andykarpov/nanit/firmware/Nanit_v2.1_1202_mod/nokia1100_lcd_font.h

//***************************************************************************
//  File........: nokia1100_lcd_lib.h
//  Author(s)...: Chiper
//  URL(s)......: http://digitalchip.ru/
//  Adapted for Nokia 2660/2760 by MadOrc
//***************************************************************************
#ifndef _NOKIA1100_LCD_FONT_H_
#define _NOKIA1100_LCD_FONT_H_

#include <avr/io.h>
#include <avr/eeprom.h>
#include <avr/pgmspace.h>

// Workaround for http://gcc.gnu.org/bugzilla/show_bug.cgi?id=34734
#ifdef PROGMEM
#undef PROGMEM
#define PROGMEM __attribute__((section(".progmem.data")))
#endif

#ifndef EEMEM
#define EEMEM__attribute__ ((section (".eeprom")))
#endif

//***************************************************************************
// Формат символов: 5x8. Установленный бит соответствует включенному пикселю
static unsigned char EEMEM nlcd_Font[][5] ={
//static const unsigned char nlcd_Font[][5] PROGMEM ={
	{0x00, 0x00, 0x00, 0x00, 0x00},// (space)
	{0x00, 0x00, 0x5F, 0x00, 0x00},// !
	{0x00, 0x00, 0x3C, 0x3C, 0x3C}, //bl " 
//	{0x00, 0x07, 0x00, 0x07, 0x00},// "
	{0x1C, 0x1C, 0x7F, 0x7F, 0x7F},// battL // #	
	{0x7F, 0x7F, 0x7F, 0x3E, 0x00},// battR //$
//	{0x14, 0x7F, 0x14, 0x7F, 0x14},// #
//	{0x24, 0x2A, 0x7F, 0x2A, 0x12},// $
	{0x23, 0x13, 0x08, 0x64, 0x62},// %
	{0x41, 0x22, 0x14, 0x08, 0x00},// > //& 
//	{0x36, 0x49, 0x55, 0x22, 0x50},// &
	{0x00, 0x05, 0x03, 0x00, 0x00},// '
	{0x00, 0x00, 0x7F, 0x41, 0x41},// [ // (
	{0x41, 0x41, 0x7F, 0x00, 0x00},// ] // )
//	{0x00, 0x1C, 0x22, 0x41, 0x00},// (
//	{0x00, 0x41, 0x22, 0x1C, 0x00},// )
	{0x08, 0x2A, 0x1C, 0x2A, 0x08},// *
	{0x08, 0x08, 0x3E, 0x08, 0x08},// +
	{0x00, 0x50, 0x30, 0x00, 0x00},// ,
	{0x08, 0x08, 0x08, 0x08, 0x08},// -
	{0x00, 0x30, 0x30, 0x00, 0x00},// .
	{0x20, 0x10, 0x08, 0x04, 0x02},// /
	{0x3E, 0x51, 0x49, 0x45, 0x3E},// 0
	{0x00, 0x42, 0x7F, 0x40, 0x00},// 1
	{0x42, 0x61, 0x51, 0x49, 0x46},// 2
	{0x21, 0x41, 0x45, 0x4B, 0x31},// 3
	{0x18, 0x14, 0x12, 0x7F, 0x10},// 4
	{0x27, 0x45, 0x45, 0x45, 0x39},// 5
	{0x3C, 0x4A, 0x49, 0x49, 0x30},// 6
	{0x01, 0x71, 0x09, 0x05, 0x03},// 7
	{0x36, 0x49, 0x49, 0x49, 0x36},// 8
	{0x06, 0x49, 0x49, 0x29, 0x1E},// 9
	{0x00, 0x36, 0x36, 0x00, 0x00},// :
/*	{0x00, 0x56, 0x36, 0x00, 0x00},// ;
	{0x00, 0x08, 0x14, 0x22, 0x41},// <
	{0x14, 0x14, 0x14, 0x14, 0x14},// =
	{0x41, 0x22, 0x14, 0x08, 0x00},// >
	{0x02, 0x01, 0x51, 0x09, 0x06},// ?
	{0x32, 0x49, 0x79, 0x41, 0x3E},// @
	{0x7E, 0x11, 0x11, 0x11, 0x7E},// A
	{0x7F, 0x49, 0x49, 0x49, 0x36},// B
	{0x3E, 0x41, 0x41, 0x41, 0x22},// C
	{0x7F, 0x41, 0x41, 0x22, 0x1C},// D
	{0x7F, 0x49, 0x49, 0x49, 0x41},// E
	{0x7F, 0x09, 0x09, 0x01, 0x01},// F
	{0x3E, 0x41, 0x41, 0x51, 0x32},// G
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
*/		

 	//Частично соответствует кодировке 866 до символа "п", далее - несоответствие

	{ 0x7E, 0x11, 0x11, 0x11, 0x7E },  // А
	{ 0x7F, 0x49, 0x49, 0x49, 0x33 },  // Б
	{ 0x7F, 0x49, 0x49, 0x49, 0x36 },  // В
	{ 0x7F, 0x01, 0x01, 0x01, 0x03 },  // Г
	{ 0xE0, 0x51, 0x4F, 0x41, 0xFF },  // Д
	{ 0x7F, 0x49, 0x49, 0x49, 0x49 },  // Е
	{ 0x77, 0x08, 0x7F, 0x08, 0x77 },  // Ж
	{ 0x49, 0x49, 0x49, 0x49, 0x36 },  // З
	{ 0x7F, 0x10, 0x08, 0x04, 0x7F },  // И
	{ 0x7C, 0x21, 0x12, 0x09, 0x7C },  // Й
	{ 0x7F, 0x08, 0x14, 0x22, 0x41 },  // К
	{ 0x20, 0x41, 0x3F, 0x01, 0x7F },  // Л
	{ 0x7F, 0x02, 0x0C, 0x02, 0x7F },  // М
	{ 0x7F, 0x08, 0x08, 0x08, 0x7F },  // Н
	{ 0x3E, 0x41, 0x41, 0x41, 0x3E },  // О
	{ 0x7F, 0x01, 0x01, 0x01, 0x7F },  // П
	{ 0x7F, 0x09, 0x09, 0x09, 0x06 },  // Р
	{ 0x3E, 0x41, 0x41, 0x41, 0x22 },  // С
	{ 0x01, 0x01, 0x7F, 0x01, 0x01 },  // Т
	{ 0x27, 0x48, 0x48, 0x48, 0x3F },  // У
	{ 0x1C, 0x22, 0x7F, 0x22, 0x1C },  // Ф
	{ 0x63, 0x14, 0x08, 0x14, 0x63 },  // Х
	{ 0x7F, 0x40, 0x40, 0x40, 0xFF },  // Ц
	{ 0x07, 0x08, 0x08, 0x08, 0x7F },  // Ч
	{ 0x7F, 0x40, 0x7F, 0x40, 0x7F },  // Ш
	{ 0x7F, 0x40, 0x7F, 0x40, 0xFF },  // Щ
	{ 0x01, 0x7F, 0x48, 0x48, 0x30 },  // Ъ
	{ 0x7F, 0x48, 0x30, 0x00, 0x7F },  // Ы
	{ 0x7F, 0x48, 0x48, 0x30, 0x00 },  // Ь
	{ 0x22, 0x41, 0x49, 0x49, 0x3E },  // Э
	{ 0x7F, 0x08, 0x3E, 0x41, 0x3E },  // Ю
	{ 0x46, 0x29, 0x19, 0x09, 0x7F },  // Я
	{ 0x20, 0x54, 0x54, 0x54, 0x78 },  // а
	{ 0x3C, 0x4A, 0x4A, 0x49, 0x31 },  // б
	{ 0x7C, 0x54, 0x54, 0x28, 0x00 },  // в
	{ 0x7C, 0x04, 0x04, 0x04, 0x0C },  // г
	{ 0xE0, 0x54, 0x4C, 0x44, 0xFC },  // д
	{ 0x38, 0x54, 0x54, 0x54, 0x08 },  // е
	{ 0x6C, 0x10, 0x7C, 0x10, 0x6C },  // ж
	{ 0x44, 0x44, 0x54, 0x54, 0x28 },  // з
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

};
static const unsigned char nlcd_12x16_Font[][24] PROGMEM ={
  // 0x20 - пробел (пустое знакоместо).
//{  0x00, 0x00, 0x00, 0x00, 0x00, 0x00, 0x00, 0x00, 0x00, 0x00, 0x00, 0x00,
//  0x00, 0x00, 0x00, 0x00, 0x00, 0x00, 0x00, 0x00, 0x00, 0x00, 0x00, 0x00},

  // 0x30 - '0'.
{  0x00, 0xf8, 0xfe, 0x06, 0x03, 0x83, 0xc3, 0x63, 0x33, 0x1e, 0xfe, 0xf8,
  0x00, 0x07, 0x1f, 0x1e, 0x33, 0x31, 0x30, 0x30, 0x30, 0x18, 0x1f, 0x07},

  // 0x31 - '1'.
{  0x00, 0x00, 0x00, 0x0c, 0x0c, 0x0e, 0xff, 0xff, 0x00, 0x00, 0x00, 0x00,
  0x00, 0x00, 0x00, 0x30, 0x30, 0x30, 0x3f, 0x3f, 0x30, 0x30, 0x30, 0x00},

  // 0x32 - '2'.
{  0x00, 0x1c, 0x1e, 0x07, 0x03, 0x03, 0x83, 0xc3, 0xe3, 0x77, 0x3e, 0x1c,
  0x00, 0x30, 0x38, 0x3c, 0x3e, 0x37, 0x33, 0x31, 0x30, 0x30, 0x30, 0x30},

  // 0x33 - '3'.
{  0x00, 0x0c, 0x0e, 0x07, 0xc3, 0xc3, 0xc3, 0xc3, 0xc3, 0xe7, 0x7e, 0x3c,
  0x00, 0x0c, 0x1c, 0x38, 0x30, 0x30, 0x30, 0x30, 0x30, 0x39, 0x1f, 0x0e},

  // 0x34 - '4'.
{  0x00, 0xc0, 0xe0, 0x70, 0x38, 0x1c, 0x0e, 0x07, 0xff, 0xff, 0x00, 0x00,
  0x00, 0x03, 0x03, 0x03, 0x03, 0x03, 0x03, 0x03, 0x3f, 0x3f, 0x03, 0x03},

  // 0x35 - '5'.
{  0x00, 0x3f, 0x7f, 0x63, 0x63, 0x63, 0x63, 0x63, 0x63, 0xe3, 0xc3, 0x83,
  0x00, 0x0c, 0x1c, 0x38, 0x30, 0x30, 0x30, 0x30, 0x30, 0x38, 0x1f, 0x0f},

  // 0x36 - '6'.
{  0x00, 0xc0, 0xf0, 0xf8, 0xdc, 0xce, 0xc7, 0xc3, 0xc3, 0xc3, 0x80, 0x00,
  0x00, 0x0f, 0x1f, 0x39, 0x30, 0x30, 0x30, 0x30, 0x30, 0x39, 0x1f, 0x0f},

  // 0x37 - '7'.
{  0x00, 0x03, 0x03, 0x03, 0x03, 0x03, 0x03, 0xc3, 0xf3, 0x3f, 0x0f, 0x03,
  0x00, 0x00, 0x00, 0x00, 0x30, 0x3c, 0x0f, 0x03, 0x00, 0x00, 0x00, 0x00},

  // 0x38 - '8'.
{  0x00, 0x00, 0xbc, 0xfe, 0xe7, 0xc3, 0xc3, 0xc3, 0xe7, 0xfe, 0xbc, 0x00,
  0x00, 0x0f, 0x1f, 0x39, 0x30, 0x30, 0x30, 0x30, 0x30, 0x39, 0x1f, 0x0f},

  // 0x39 - '9'.
{  0x00, 0x3c, 0x7e, 0xe7, 0xc3, 0xc3, 0xc3, 0xc3, 0xc3, 0xe7, 0xfe, 0xfc,
  0x00, 0x00, 0x00, 0x30, 0x30, 0x30, 0x38, 0x1c, 0x0e, 0x07, 0x03, 0x00},
	
};
#endif /* _NOKIA1100_LCD_FONT_H_ */
